diego-roque-gomez/Sportanzeigetafel/Ensamblaje2.SLDASM

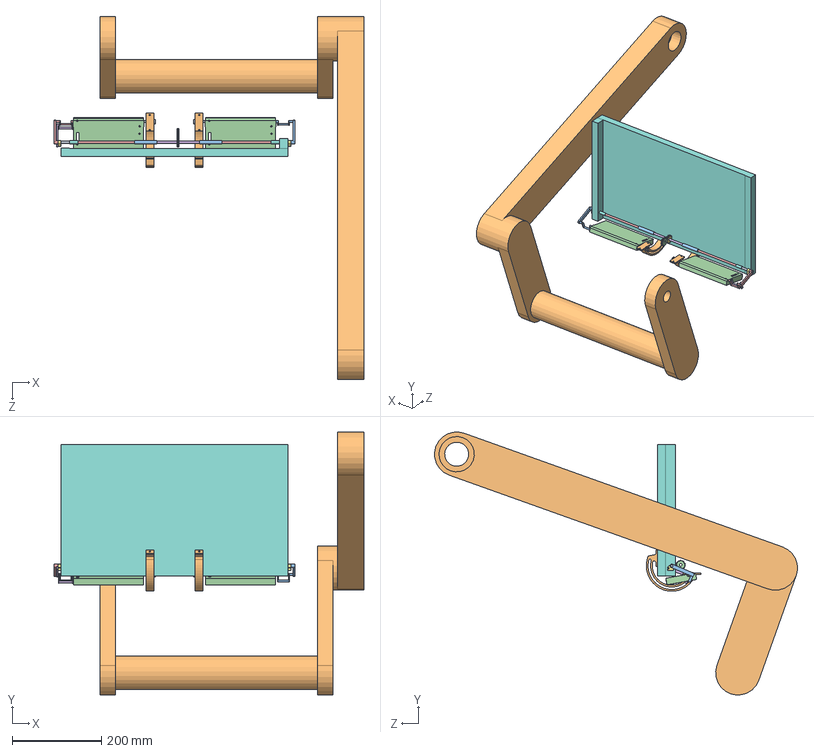
[picture p4: CAD file, 2026-02-12]
Ensamblaje2.SLDASM
696.1 x 590.7 x 815.4 mm
tabero
soporte x 2
barra izquierda 1
barra derecha 2
tablero2 x 2
barra derecha 1
barra izwuierda 2
eje pequeño x 2
seguro (2024) x 2
engrane 1
ejesote 1
ejesote x 2
engrane 2
broche x 2
Guia x 2
Soporte_nuevo253 x 2
