diego-roque-gomez/Sportanzeigetafel/Hardware/CAD/Soporte_nuevo224.SLDPRT

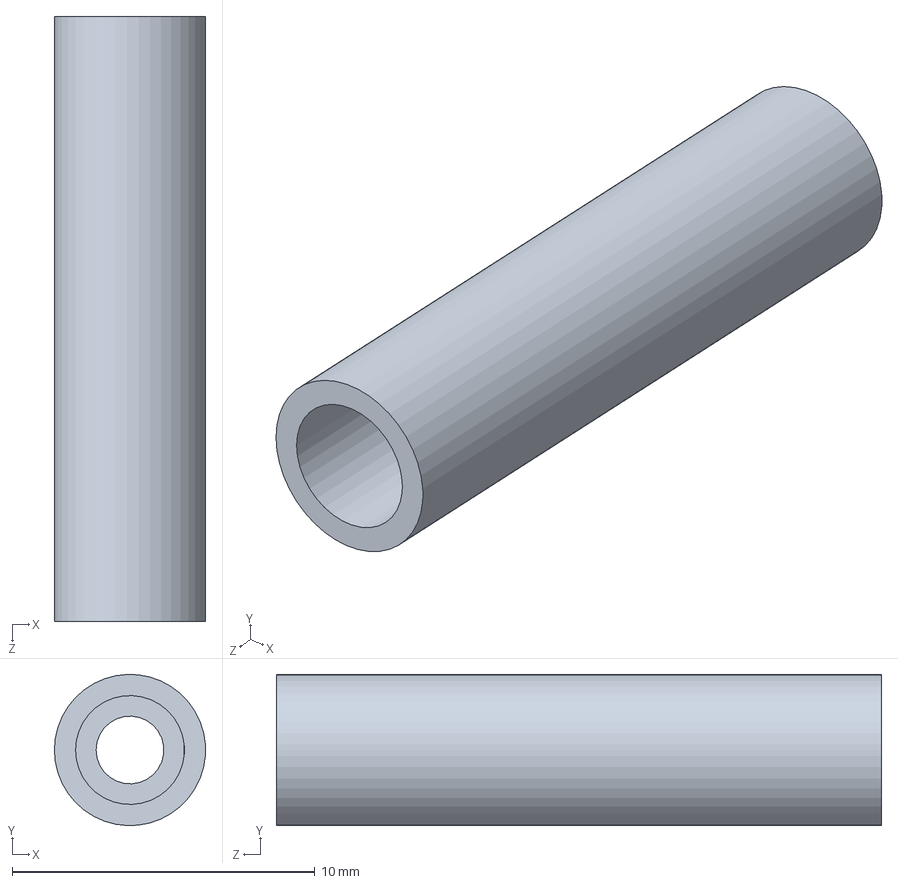
[picture p19: CAD file, 2026-02-12]
Hardware/CAD/Soporte_nuevo224.SLDPRT
5.00 x 5.00 x 20.0 mm
