diego-roque-gomez/Sportanzeigetafel/Hardware/CAD/Soporte_nuevo253.SLDPRT

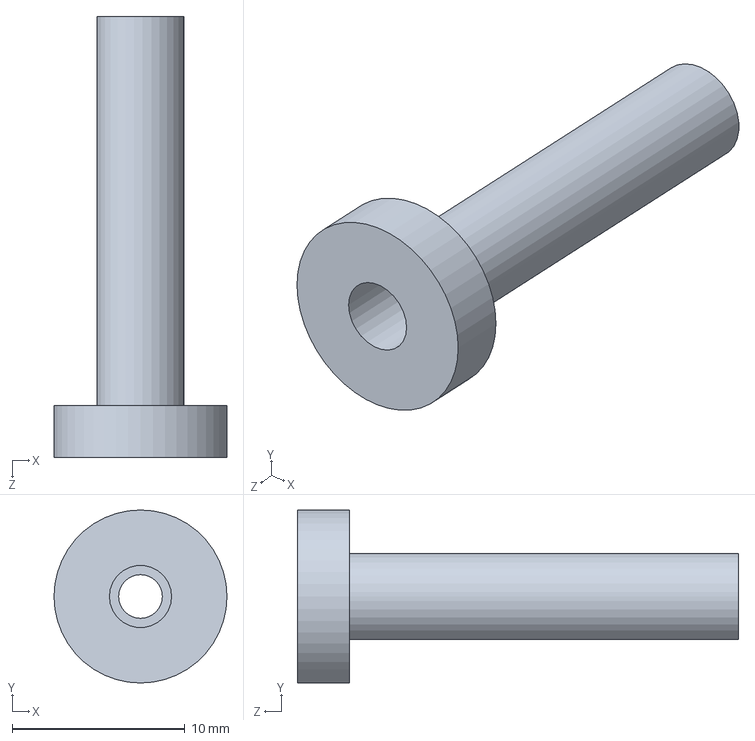
[picture p20: CAD file, 2026-02-12]
Hardware/CAD/Soporte_nuevo253.SLDPRT
10.0 x 10.0 x 25.5 mm
