diego-roque-gomez/Sportanzeigetafel/Hardware/CAD/tablero2.SLDPRT

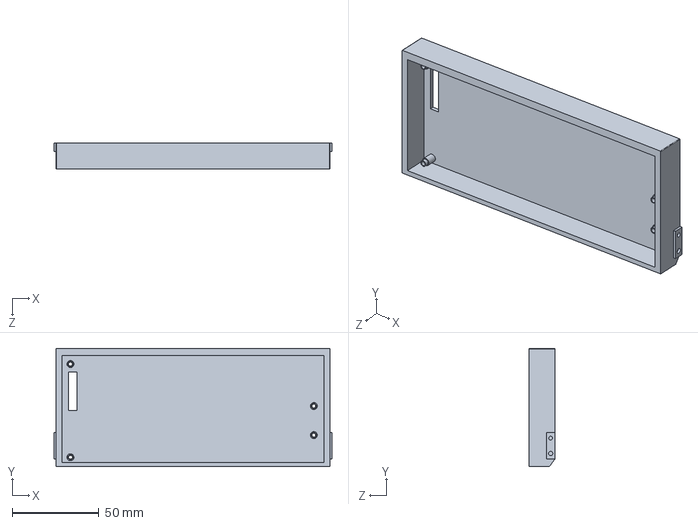
[picture p21: CAD file, 2026-02-12]
Hardware/CAD/tablero2.SLDPRT
160.0 x 68.0 x 15.0 mm
